alberto-rota/LoopStation-DIY-Project/Looper Controller MIDI/src/lcd_bar_chars.h

#include <Arduino.h>

byte zero[] = {  
  B00000,
  B00000,
  B00000,
  B00000,
  B00000,
  B00000,
  B00000,
  B00000
};
byte one[] = {
  B10000,
  B10000,
  B10000,
  B10000,
  B10000,
  B10000,
  B10000,
  B10000
};

byte two[] = {
  B11000,
  B11000,
  B11000,
  B11000,
  B11000,
  B11000,
  B11000,
  B11000
};

byte three[] = {
  B11100,
  B11100,
  B11100,
  B11100,
  B11100,
  B11100,
  B11100,
  B11100
};

byte four[] = {
  B11110,
  B11110,
  B11110,
  B11110,
  B11110,
  B11110,
  B11110,
  B11110
};

byte five[] = {
  B11111,
  B11111,
  B11111,
  B11111,
  B11111,
  B11111,
  B11111,
  B11111
};
